StoweWilson/Blueprint_keyboard/images/keypad sch.png

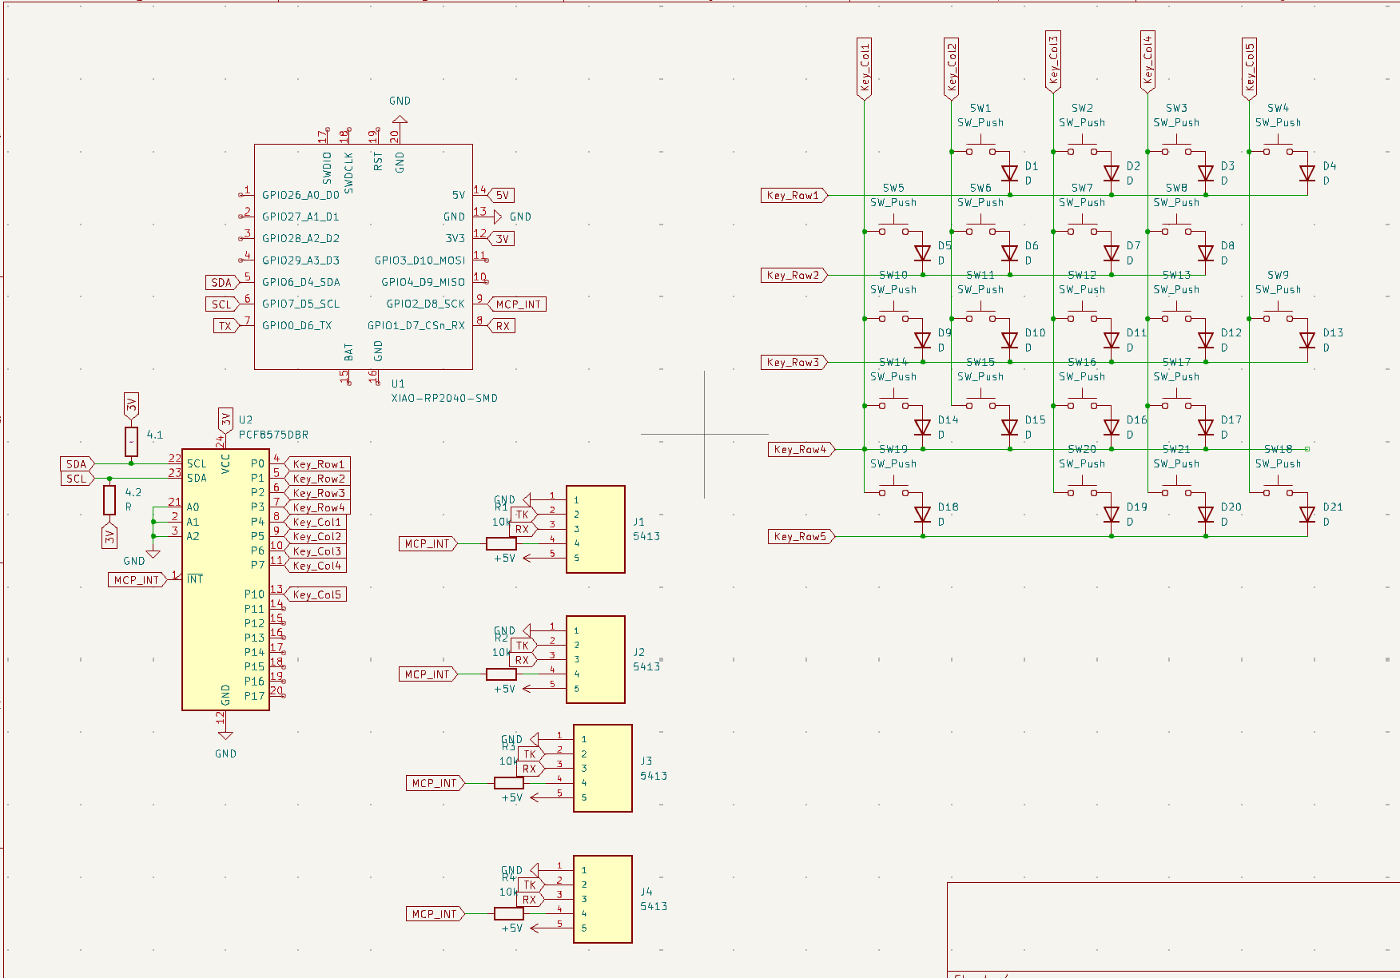
images/keypad sch.png
